Brunius/BruPit/MCAD/LaserCut/ButtonBox-Bottomplate.SLDPRT

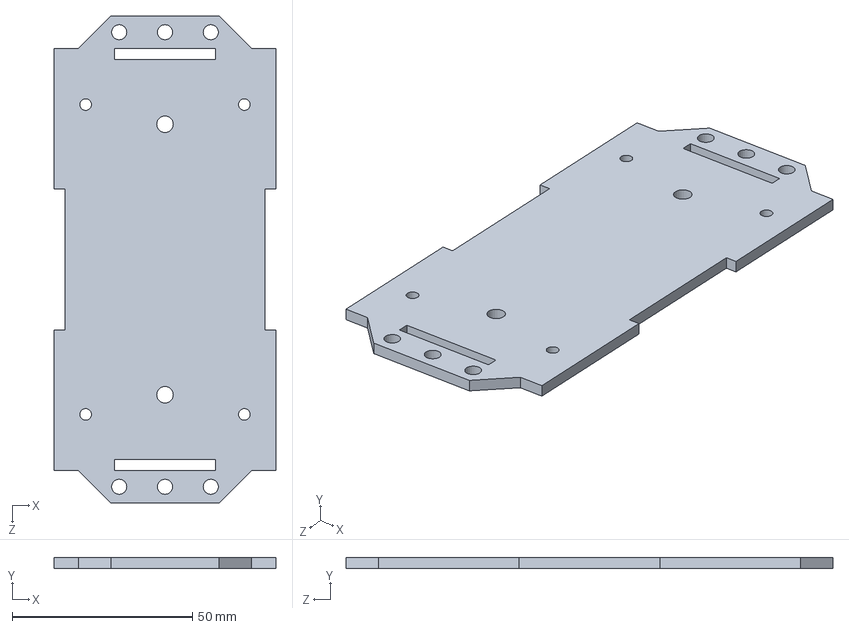
[picture p15: CAD file, 2022-02-06]
MCAD/LaserCut/ButtonBox-Bottomplate.SLDPRT
61.5 x 3.00 x 135.0 mm
