Brunius/BruPit/MCAD/Master-BottomTop.SLDPRT

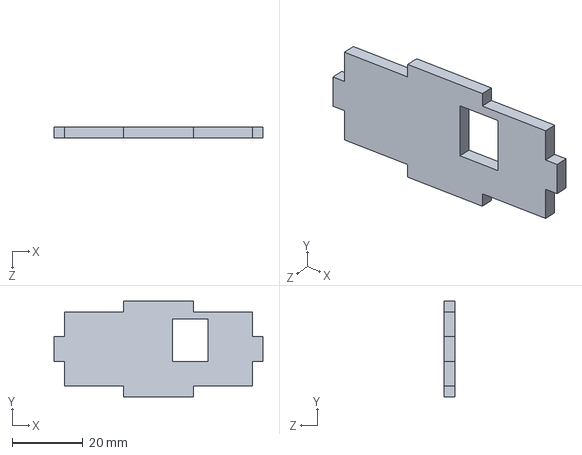
[picture p16: CAD file, 2022-02-04]
MCAD/Master-BottomTop.SLDPRT
59.0 x 27.0 x 3.00 mm
