Brunius/BruPit/MCAD/Junction-Back.SLDPRT

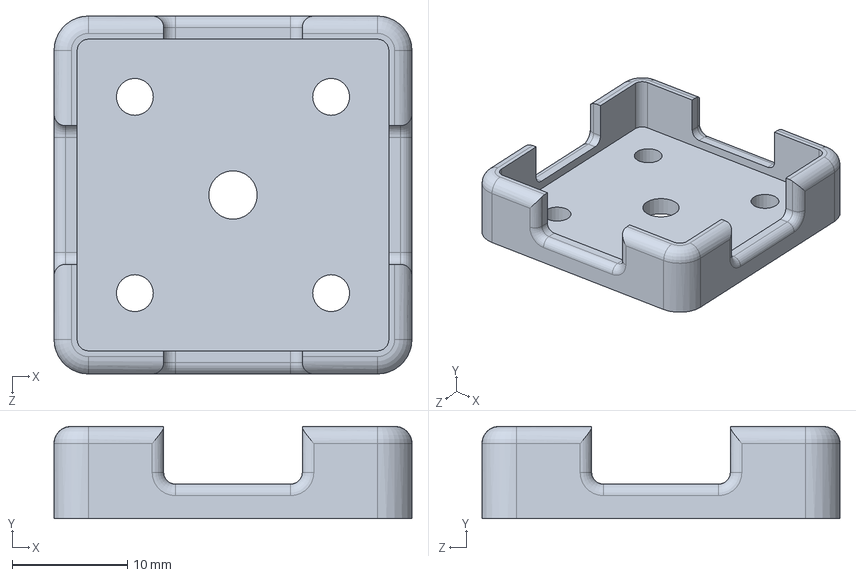
[picture p17: CAD file, 2022-02-04]
MCAD/Junction-Back.SLDPRT
31.0 x 8.00 x 31.0 mm
