Brunius/BruPit/MCAD/LaserCut/Master-BottomTop.DXF

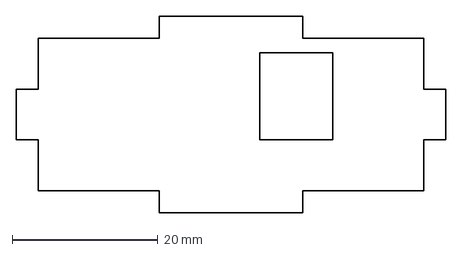
[picture p18: CAD file, 2022-02-06]
MCAD/LaserCut/Master-BottomTop.DXF
59.0 x 27.0 mm
