Brunius/BruPit/MCAD/Frontside.SLDPRT

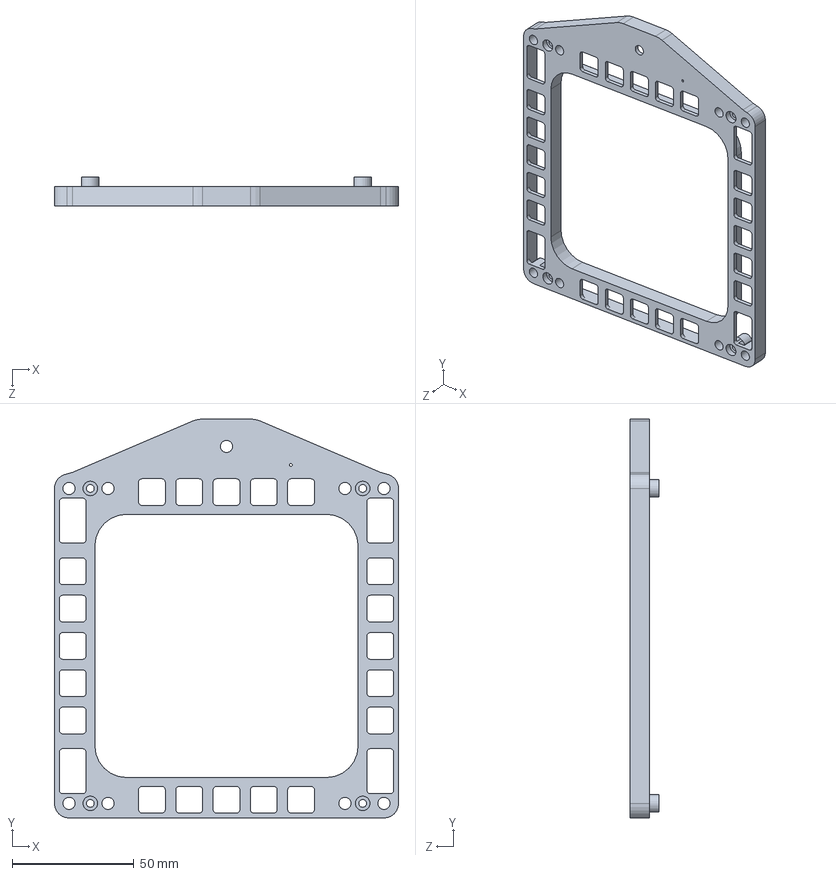
[picture p19: CAD file, 2022-02-04]
MCAD/Frontside.SLDPRT
141.2 x 163.7 x 12.0 mm
