Brunius/BruPit/MCAD/LaserCut/SwitchBox-Faceplate.SLDPRT

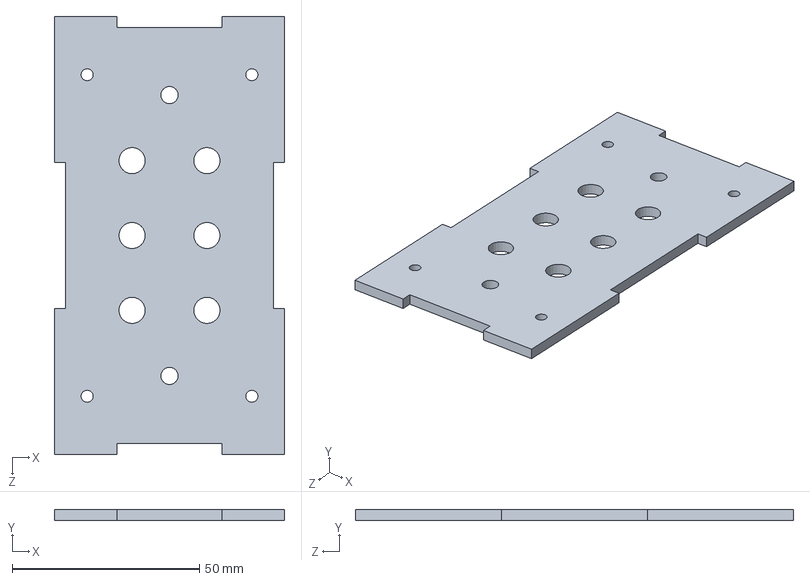
[picture p20: CAD file, 2022-02-04]
MCAD/LaserCut/SwitchBox-Faceplate.SLDPRT
61.5 x 3.00 x 117.0 mm
