Brunius/BruPit/MCAD/Backside.SLDPRT

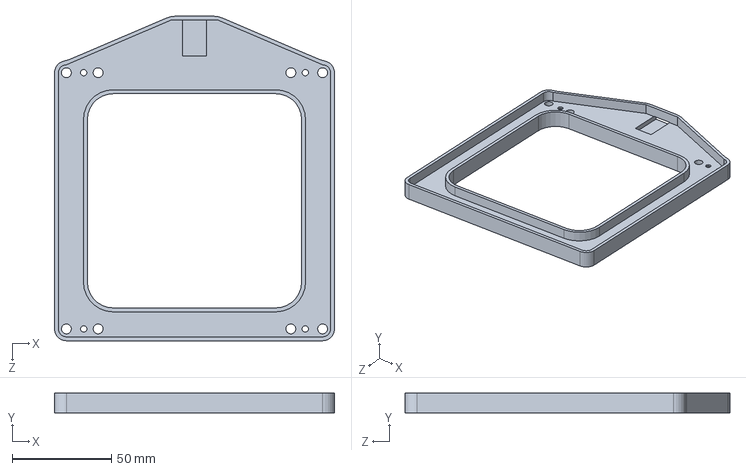
[picture p22: CAD file, 2022-02-04]
MCAD/Backside.SLDPRT
141.2 x 10.0 x 163.7 mm
