Brunius/BruPit/MCAD/LaserCut/MFD-Layer1.SLDPRT

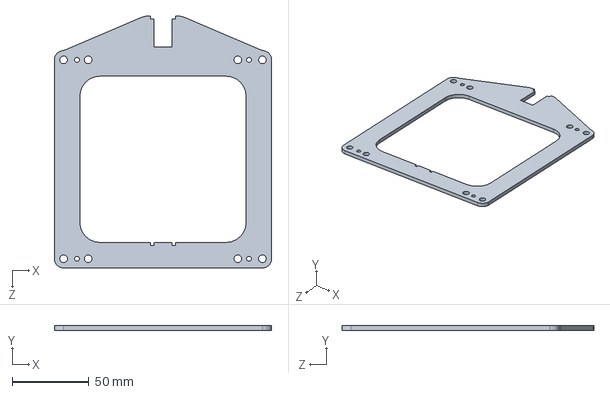
[picture p23: CAD file, 2022-02-04]
MCAD/LaserCut/MFD-Layer1.SLDPRT
141.2 x 3.00 x 163.7 mm
