Brunius/BruPit/MCAD/LaserCut/UFC-Faceplate.SLDPRT

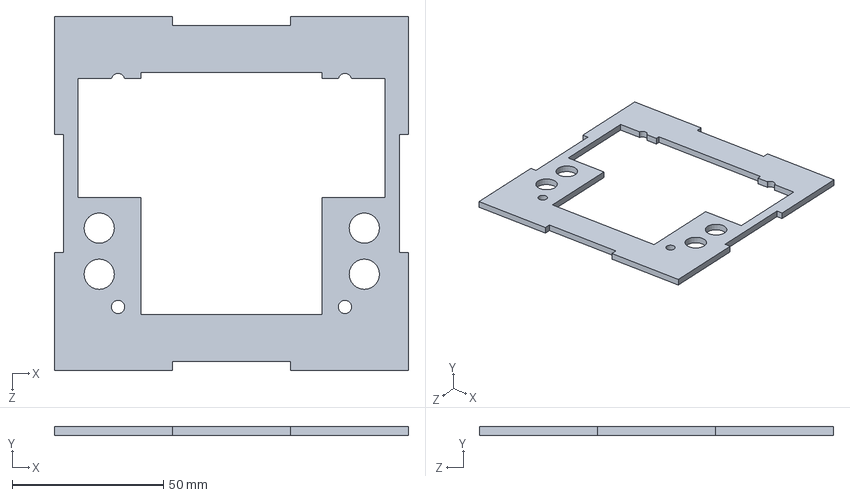
[picture p24: CAD file, 2022-02-04]
MCAD/LaserCut/UFC-Faceplate.SLDPRT
117.0 x 3.00 x 117.0 mm
