Brunius/BruPit/MCAD/LaserCut/SwitchBox-Sideplate.SLDPRT

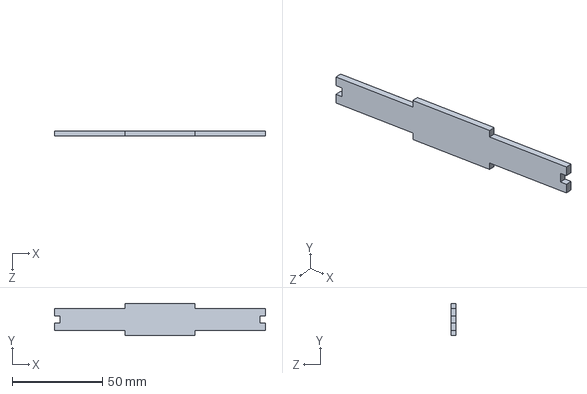
[picture p25: CAD file, 2022-02-04]
MCAD/LaserCut/SwitchBox-Sideplate.SLDPRT
117.0 x 18.0 x 3.00 mm
