Brunius/BruPit/MCAD/LongButton.SLDPRT

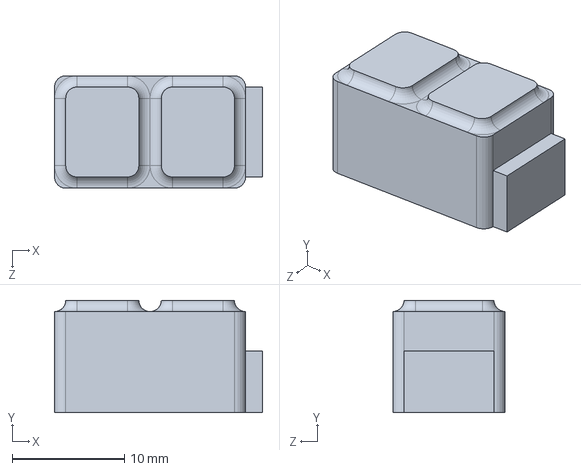
[picture p26: CAD file, 2021-07-14]
MCAD/LongButton.SLDPRT
18.5 x 10.0 x 10.0 mm
