Brunius/BruPit/MCAD/LaserCut/ButtonBox-Topplate.SLDPRT

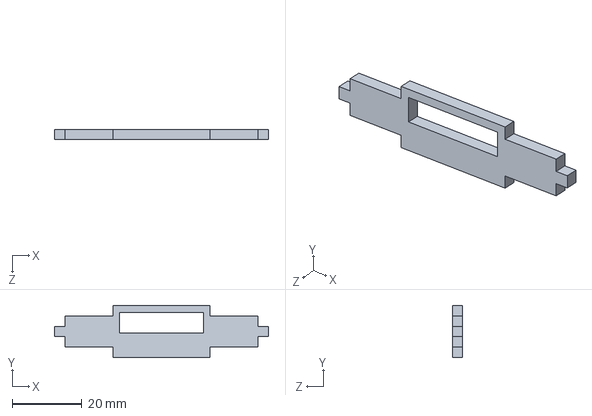
[picture p27: CAD file, 2022-02-04]
MCAD/LaserCut/ButtonBox-Topplate.SLDPRT
61.5 x 15.0 x 3.00 mm
