Brunius/BruPit/MCAD/SquareButton.SLDPRT

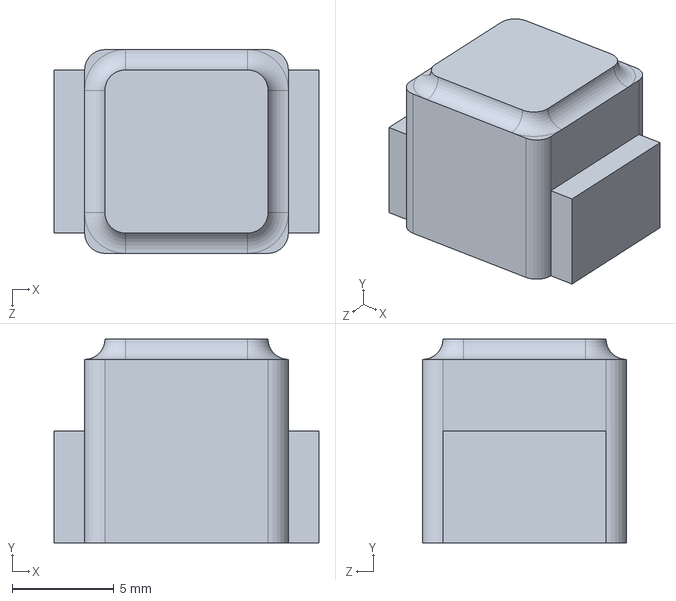
[picture p28: CAD file, 2021-07-14]
MCAD/SquareButton.SLDPRT
13.0 x 10.0 x 10.0 mm
