Brunius/BruPit/MCAD/LaserCut/UFC-TopPlate.SLDPRT

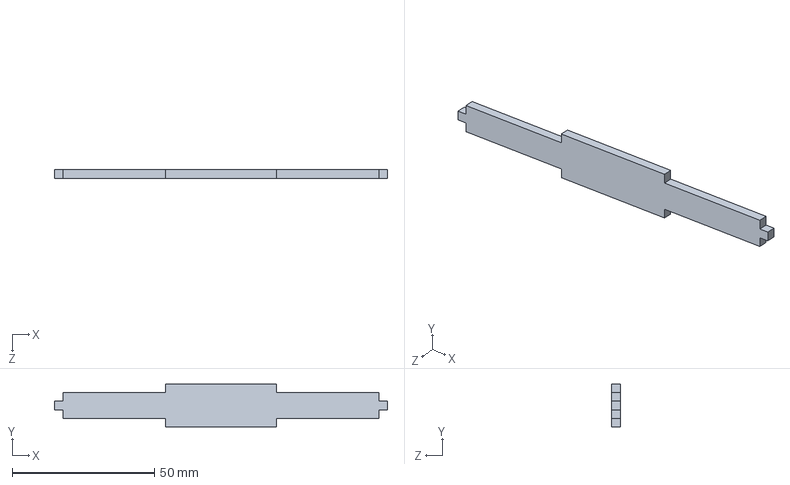
[picture p29: CAD file, 2022-02-04]
MCAD/LaserCut/UFC-TopPlate.SLDPRT
117.0 x 15.0 x 3.00 mm
