Brunius/BruPit/MCAD/LaserCut/SwitchBox-Topplate.SLDPRT

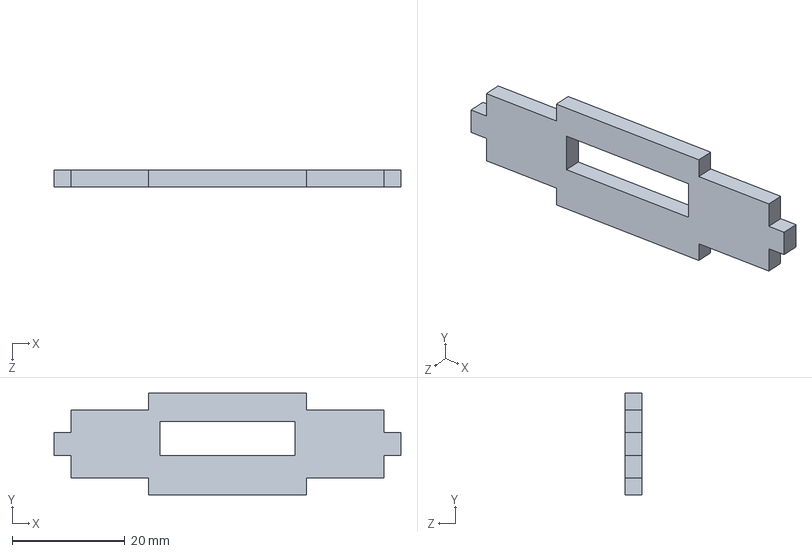
[picture p30: CAD file, 2022-02-04]
MCAD/LaserCut/SwitchBox-Topplate.SLDPRT
61.5 x 18.0 x 3.00 mm
