Brunius/BruPit/MCAD/LaserCut/UFC-Backplate.SLDPRT

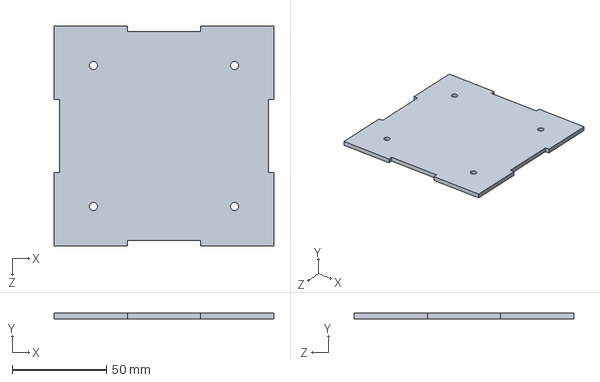
[picture p31: CAD file, 2022-02-04]
MCAD/LaserCut/UFC-Backplate.SLDPRT
117.0 x 3.00 x 117.0 mm
