Brunius/BruPit/MCAD/LaserCut/MFD-Layer4.SLDPRT

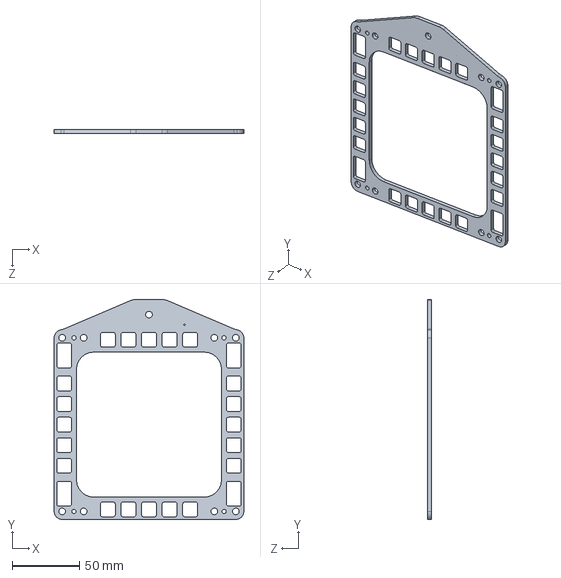
[picture p32: CAD file, 2022-02-04]
MCAD/LaserCut/MFD-Layer4.SLDPRT
141.2 x 163.7 x 3.00 mm
