Brunius/BruPit/MCAD/LaserCut/ButtonBox-Faceplate.SLDPRT

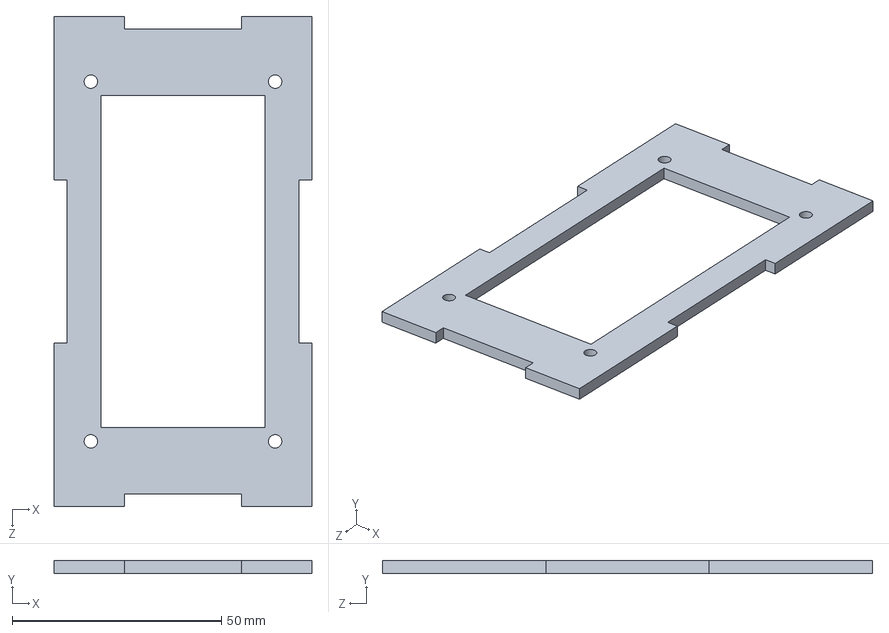
[picture p33: CAD file, 2022-02-04]
MCAD/LaserCut/ButtonBox-Faceplate.SLDPRT
61.5 x 3.00 x 117.0 mm
