Brunius/BruPit/MCAD/LaserCut/MFD-locking.SLDPRT

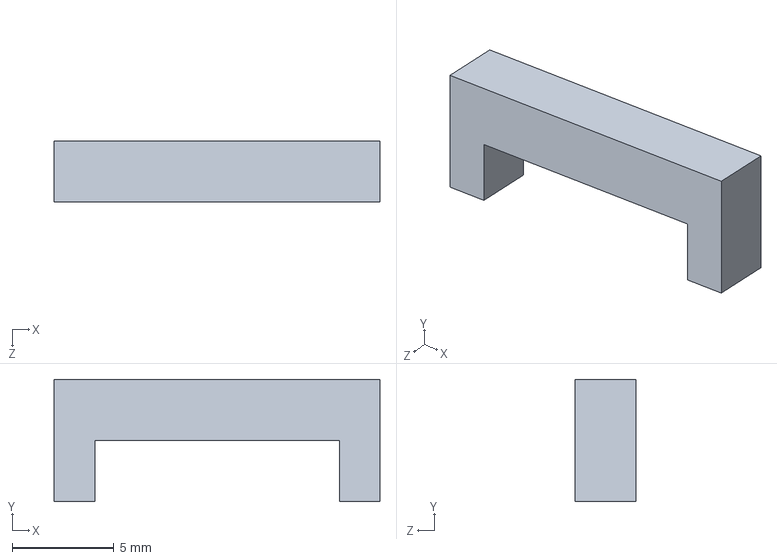
[picture p34: CAD file, 2022-02-04]
MCAD/LaserCut/MFD-locking.SLDPRT
16.0 x 6.00 x 3.00 mm
