Brunius/BruPit/MCAD/LaserCut/MFD-Layer3.SLDPRT

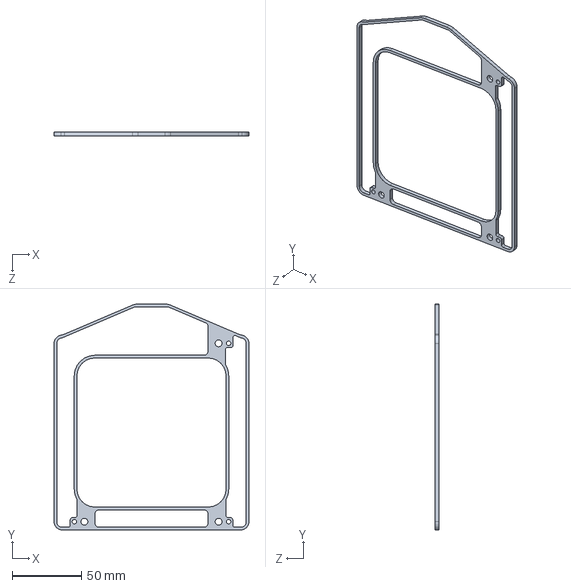
[picture p35: CAD file, 2022-02-04]
MCAD/LaserCut/MFD-Layer3.SLDPRT
141.2 x 163.7 x 3.00 mm
