Brunius/BruPit/MCAD/LaserCut/UFC-BottomPlate.SLDPRT

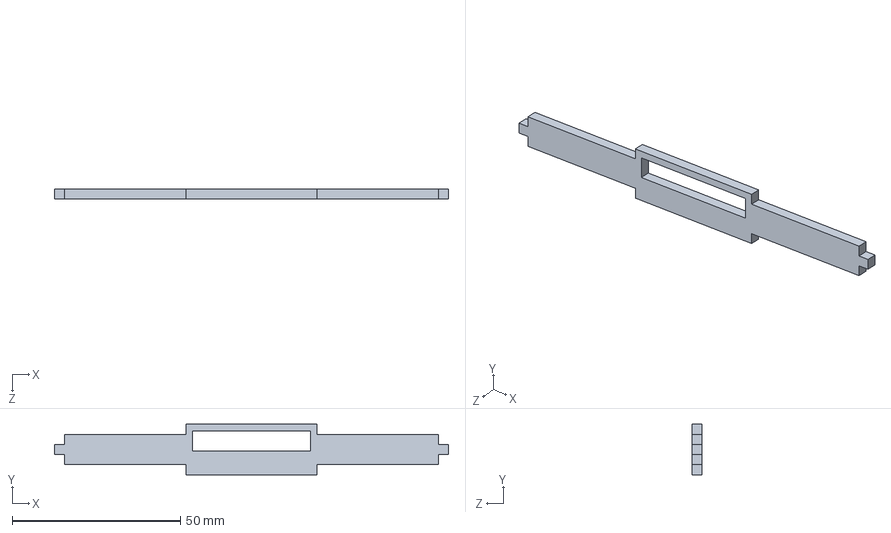
[picture p36: CAD file, 2022-02-04]
MCAD/LaserCut/UFC-BottomPlate.SLDPRT
117.0 x 15.0 x 3.00 mm
