Brunius/BruPit/MCAD/LaserCut/UFC-Sideplate.SLDPRT

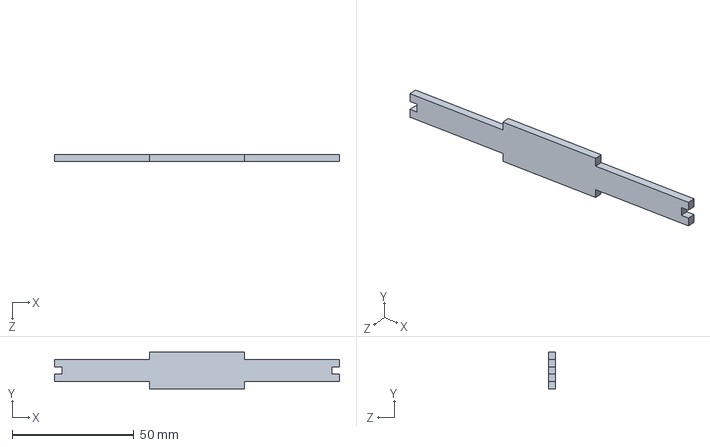
[picture p37: CAD file, 2022-02-04]
MCAD/LaserCut/UFC-Sideplate.SLDPRT
117.0 x 15.0 x 3.00 mm
